deuteros76/meteo-home/docs/assets/images/breadboard.jpg

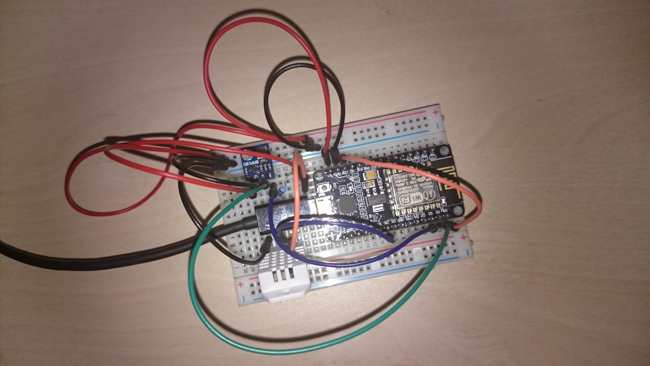
docs/assets/images/breadboard.jpg
