deuteros76/meteo-home/docs/assets/images/devboards.JPG

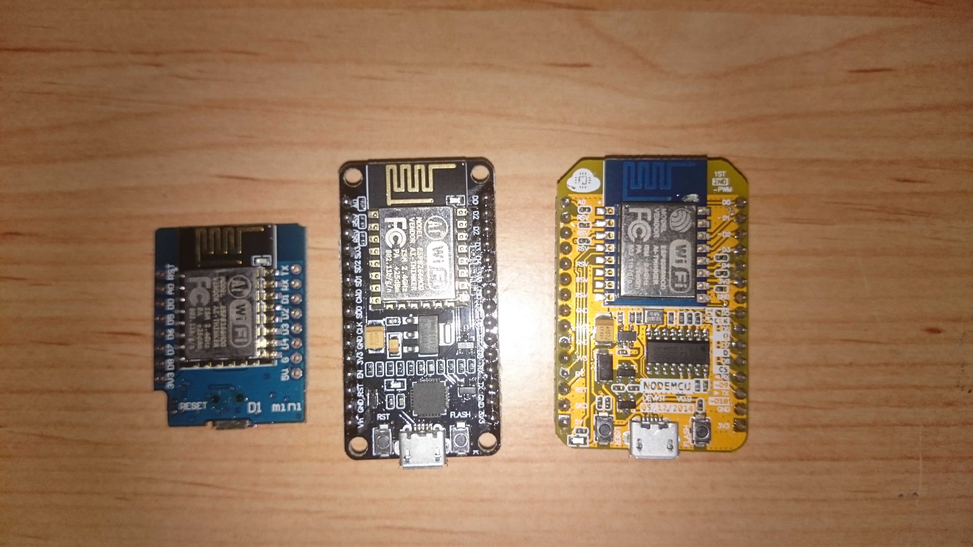
docs/assets/images/devboards.JPG
