deuteros76/meteo-home/docs/assets/images/has-meteohome-weather-ext.png

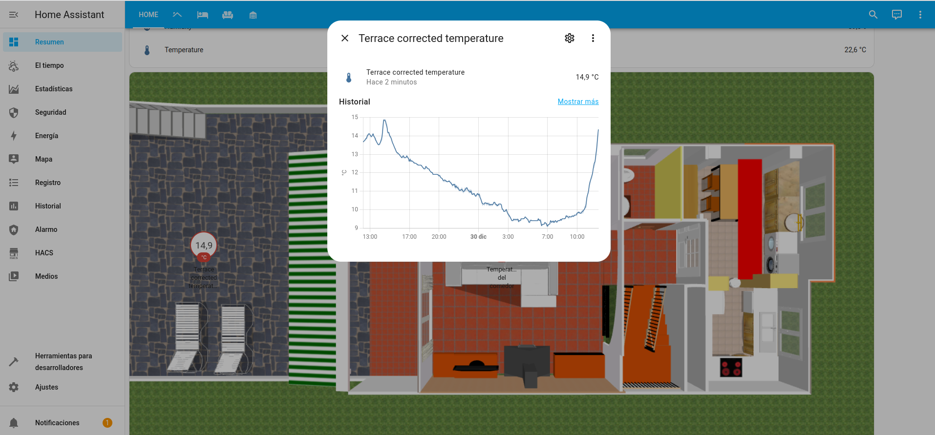
docs/assets/images/has-meteohome-weather-ext.png
