deuteros76/meteo-home/docs/assets/images/meteo-home_bb.png

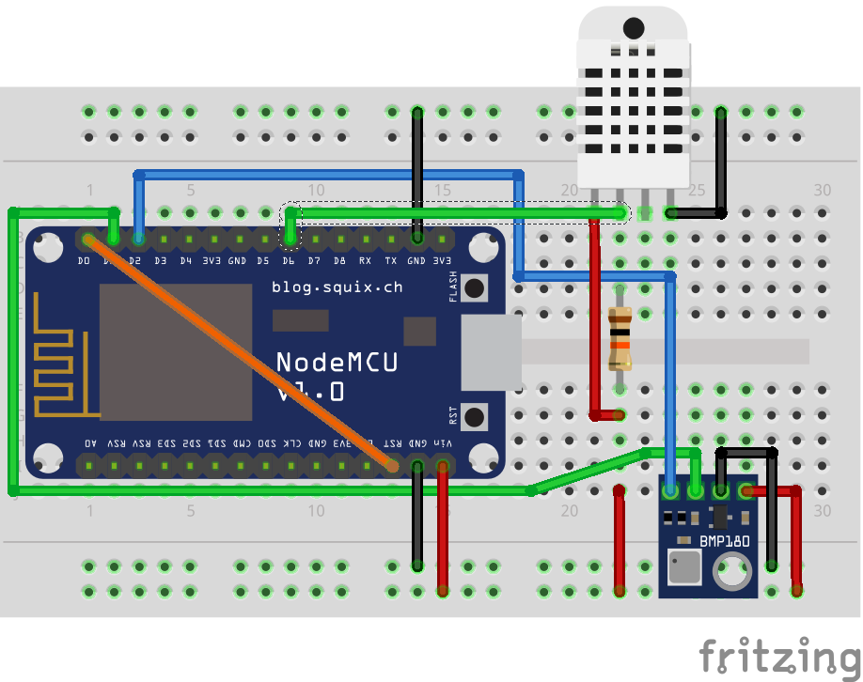
docs/assets/images/meteo-home_bb.png
