deuteros76/meteo-home/docs/assets/images/home-assistant-history.png

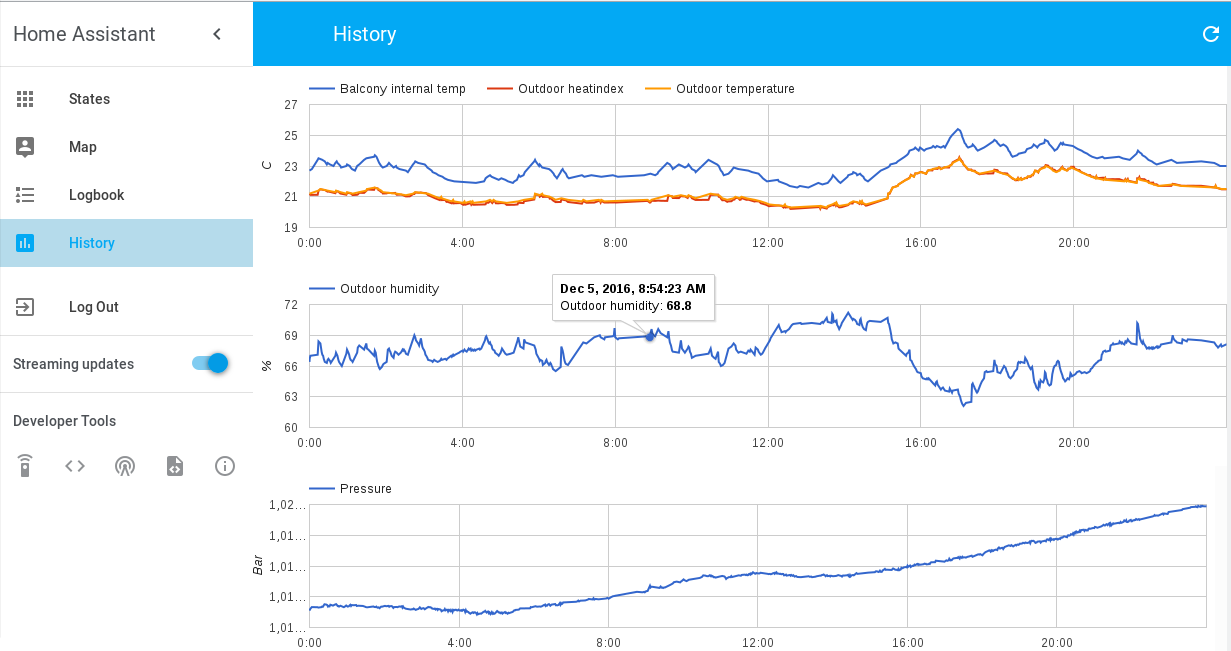
docs/assets/images/home-assistant-history.png
