deuteros76/meteo-home/src/mhsgp30.cpp

/*
Copyright 2023 meteo-home

Licensed under the Apache License, Version 2.0 (the "License");
you may not use this file except in compliance with the License.
You may obtain a copy of the License at

    http://www.apache.org/licenses/LICENSE-2.0

Unless required by applicable law or agreed to in writing, software
distributed under the License is distributed on an "AS IS" BASIS,
WITHOUT WARRANTIES OR CONDITIONS OF ANY KIND, either express or implied.
See the License for the specific language governing permissions and
limitations under the License.
*/ 

#include "mhsgp30.hpp"

MHSGP30::MHSGP30(MeteoBoard *p, Manager *m, Leds *l) : SGP30(), leds(l)
{
  manager = m;
  parent = p;
  co2_discovery_topic = String("homeassistant/sensor/ESP-" + String(ESP.getChipId()) +"/SGP30-CO2/config");
  voc_discovery_topic = String("homeassistant/sensor/ESP-" + String(ESP.getChipId()) + "/SGP30-VOC/config");

  sensorReady=false;
}

bool MHSGP30::begin(TwoWire &wirePort){
  if (manager == nullptr){
    sensorReady = false;
  }else if (SGP30::begin(wirePort)){
    sensorReady= true;
    initAirQuality();
    Serial.println("[SGP30] reading baseline.");
    readBaseline();

    co2_topic = manager->deviceName() + "/SGP30/co2";
    voc_topic = manager->deviceName() + "/SGP30/voc";
  }else{     
    Serial.println("[SGP30] Error initializing SGP30 sensor.");
    sensorReady= false;
  }
  if(leds == nullptr){
    //throw std::invalid_argument("service must not be null");
    sensorReady = false;
  }  

  return sensorReady;
}

bool MHSGP30::available(){
  if (!sensorReady){
    return false;
  }
  // Re-probe the sensor on the I2C bus to detect a runtime disconnection so the
  // value stops being published and Home Assistant marks it unavailable via
  // expire_after.
  const uint8_t SGP30_I2C_ADDRESS = 0x58; // SGP30 fixed I2C address
  Wire.beginTransmission(SGP30_I2C_ADDRESS);
  return (Wire.endTransmission() == 0);
}

void MHSGP30::read(){
  //read SGP30 values
  measureAirQuality();

  float CO2 = getCO2();

  parent->getClient()->publish(getCO2Topic().c_str(), String(CO2).c_str(), true); 
  delay(50);
  parent->getClient()->publish(getVOCTopic().c_str(), String(getVOC()).c_str(), true); 
  delay(50);
     
  Serial.println("[SGP30] CO2 = " + String(CO2) + " TVOC = " + String(TVOC));
  
  saveBaseline();

  if (CO2 < 600) {
    leds->setLEDs(LOW,HIGH,LOW);
  } else if (CO2 < 800) {
    leds->setLEDs(LOW,LOW,HIGH);
  } else {
    leds->setLEDs(HIGH,LOW,LOW);
  }
}

void MHSGP30::read(float temperature, float humidity){
  if ((humidity > 0) && (temperature > 0)) {
    //Convert relative humidity to absolute humidity
    double absHumidity = RHtoAbsolute(humidity, temperature);

    //Convert the double type humidity to a fixed point 8.8bit number
    uint16_t sensHumidity = doubleToFixedPoint(absHumidity);

    //Set the humidity compensation on the SGP30 to the measured value
    //If no humidity sensor attached, sensHumidity should be 0 and sensor will use default
    setHumidity(sensHumidity);
    Serial.print("[SGP30] Absolute Humidity Compensation set to: " + String(absHumidity) +" g/m^3 ");
  }
  read();
}

String MHSGP30::getDiscoveryMsg(String deviceName, deviceClass dev_class){
  String topic, unit, className;

  switch (dev_class){
    case co2_sensor: unit = "ppm"; className="carbon_dioxide"; topic= deviceName+"/SGP30/co2"; break;
    case voc_sensor: unit = "ppb\t"; className="volatile_organic_compounds"; topic= deviceName+"/SGP30/voc"; break;
    default: break;
  }
  return createDiscoveryMsg(topic, className, unit);
}



void MHSGP30::readBaseline(){
  if (LittleFS.begin()) {
    //LittleFS.remove("/baseline.json"); // Uncomment to remove the file if the device sends extremly high values of CO2 / TVOC
    if (LittleFS.exists("/baseline.json")) {
      //file exists, reading and loading
      File blFile = LittleFS.open("/baseline.json", "r");
      if (blFile) {
        size_t size = blFile.size();
        // Allocate a buffer to store contents of the file.
        std::unique_ptr<char[]> buf(new char[size]);

        blFile.readBytes(buf.get(), size);
        DynamicJsonDocument json(1024);
        DeserializationError error =deserializeJson(json,buf.get());
        if (!error) {
          Serial.println("\n[SGP30] parsed json");          
          serializeJson(json, Serial);
        

          baselineCO2 = json["blCO2"].as<uint16_t>();;
          baselineTVOC = json["blTVOC"].as<uint16_t>();;          
          setBaseline(baselineCO2, baselineTVOC);
          Serial.println(String("\n[SGP30] Restoring baseline from file (CO2/TVOC):")+baselineCO2+"/"+baselineTVOC);
        }else{
          Serial.println("\n[SGP30] Baseline json is corrpupt.");      
        }
      }
      blFile.close();
    }else{
      Serial.println("\n[SGP30] Baseline file not found.");      
    }
  }
}

void MHSGP30::saveBaseline(){
  DynamicJsonDocument json(1024);

  getBaseline();  

  if (baselineCO2>0 && baselineTVOC>0 ){
    json["blCO2"] = String(baselineCO2);
    json["blTVOC"] = String(baselineTVOC);
    Serial.println(String("\n[SGP30] Saving new baseline values (CO2,TVOC):")+baselineCO2+"/"+baselineTVOC);
      
    File blFile = LittleFS.open("/baseline.json", "w");
    if (!blFile) {
      Serial.println("[SGP30] failed to open config file for writing");
    }
    
    serializeJson(json, blFile);
    blFile.close();
  }
 }

void MHSGP30::autodiscover(){
  if (sensorReady){
      parent->sendDiscoveryMessage(getCO2DiscoveryTopic(), getDiscoveryMsg(manager->deviceName(),MeteoSensor::deviceClass::co2_sensor));
      parent->sendDiscoveryMessage(getVOCDiscoveryTopic(), getDiscoveryMsg(manager->deviceName(), MeteoSensor::deviceClass::voc_sensor));
   }
}

double MHSGP30::RHtoAbsolute (float relHumidity, float tempC) {
  double eSat = 6.11 * pow(10.0, (7.5 * tempC / (237.7 + tempC)));
  double vaporPressure = (relHumidity * eSat) / 100; //millibars
  double absHumidity = 1000 * vaporPressure * 100 / ((tempC + 273) * 461.5); //Ideal gas law with unit conversions
  return absHumidity;
}

uint16_t MHSGP30::doubleToFixedPoint( double number) {
  int power = 1 << 8;
  double number2 = number * power;
  uint16_t value = floor(number2 + 0.5);
  return value;
}
