deuteros76/meteo-home/src/mhanalog.cpp

/*
Copyright 2023 meteo-home

Licensed under the Apache License, Version 2.0 (the "License");
you may not use this file except in compliance with the License.
You may obtain a copy of the License at

    http://www.apache.org/licenses/LICENSE-2.0

Unless required by applicable law or agreed to in writing, software
distributed under the License is distributed on an "AS IS" BASIS,
WITHOUT WARRANTIES OR CONDITIONS OF ANY KIND, either express or implied.
See the License for the specific language governing permissions and
limitations under the License.
*/ 
#include "mhanalog.hpp"

MHAnalog::MHAnalog(MeteoBoard *p, Manager *m){
  if (p == nullptr || m == nullptr) {
        Serial.println("[Analog] MeteoBoard or Manager pointer is null");
  }else {
  
    manager = m;
    parent = p;
    value_discovery_topic = "homeassistant/sensor/ESP-" + String(ESP.getChipId()) +"/Analog-value/config";

    value = 0;
    values_read = false;
  }
}

bool MHAnalog::begin(){
  bool returnValue=true;
  if (manager->sensorClass().equals("moisture"))
  {
    value_topic= manager->deviceName()+"/moisture/value";
  }else if (manager->sensorClass().equals("proximity")){
    value_topic= manager->deviceName()+"/moisture/value";
  }else{
    Serial.println("[Analog] Error: unknown sensor class");
    returnValue = false;
  }

  if (manager == nullptr){
    Serial.println("[Analog] Error: Manager is null");
    returnValue = false;
  }

  return returnValue;
}

bool MHAnalog::available(){
  bool returnValue=true;

  //! A0 will always return a value between 0 and 1024 so the return value only depends on the configuration parameter useAnalogSensor
  if (!manager->useAnalogSensor()){
    returnValue= false;
  }

  if (!returnValue){
    Serial.println("[Analog] Error initializing Analog sensor.");
  }

  return returnValue;
}

void MHAnalog::read(){
   //read Analog value
  int rawValue=analogRead(A0);
  if (manager->useAnalogSensor()){
    int minValue = manager->analogMinValue();
    int maxValue = manager->analogMaxValue();

    if (!values_read && (minValue>=0 && maxValue>=0)){ 
      value = map(rawValue, minValue, maxValue, 0, 100);  
    }
    if (value<0 || value>100) {    
        value = -1;
    }
  }

  parent->getClient()->publish(getValueTopic().c_str(), String(getValue()).c_str(), true);
  delay(50);
     
  Serial.println("[Analog] Value = " + String(getValue()) + "% ("+String(rawValue)+")" );
  values_read= false;
}

String MHAnalog::getDiscoveryMsg(String deviceName, deviceClass dev_class){
  String unit, className;

  switch (dev_class){
    case moisture_sensor: unit = "%"; className="moisture"; break;
    case proximity_sensor: unit = "mm"; className="proximity"; break;
    default: break;
  }

  return createDiscoveryMsg(getValueTopic(), className, unit);
}

void MHAnalog::autodiscover(){
  if (available()){
     manager->sensorClass().toLowerCase();
     if (manager->sensorClass().equals("moisture"))
     {
      parent->sendDiscoveryMessage(getValueDiscoveryTopic(), getDiscoveryMsg(manager->deviceName(),MeteoSensor::deviceClass::moisture_sensor));    
     }else if (manager->sensorClass().equals("proximity"))
     {
      parent->sendDiscoveryMessage(getValueDiscoveryTopic(), getDiscoveryMsg(manager->deviceName(),MeteoSensor::deviceClass::proximity_sensor));    
     }else{
      Serial.println("[Analog] Error identifying an analog sensor");
     }     
  }
}
